csmith1188/eBankMachine/Schematics/kicad/eBankMachine.kicad_pcb

## KiCad design hardware/kicad/boards/07_alu/07_alu.kicad_pcb

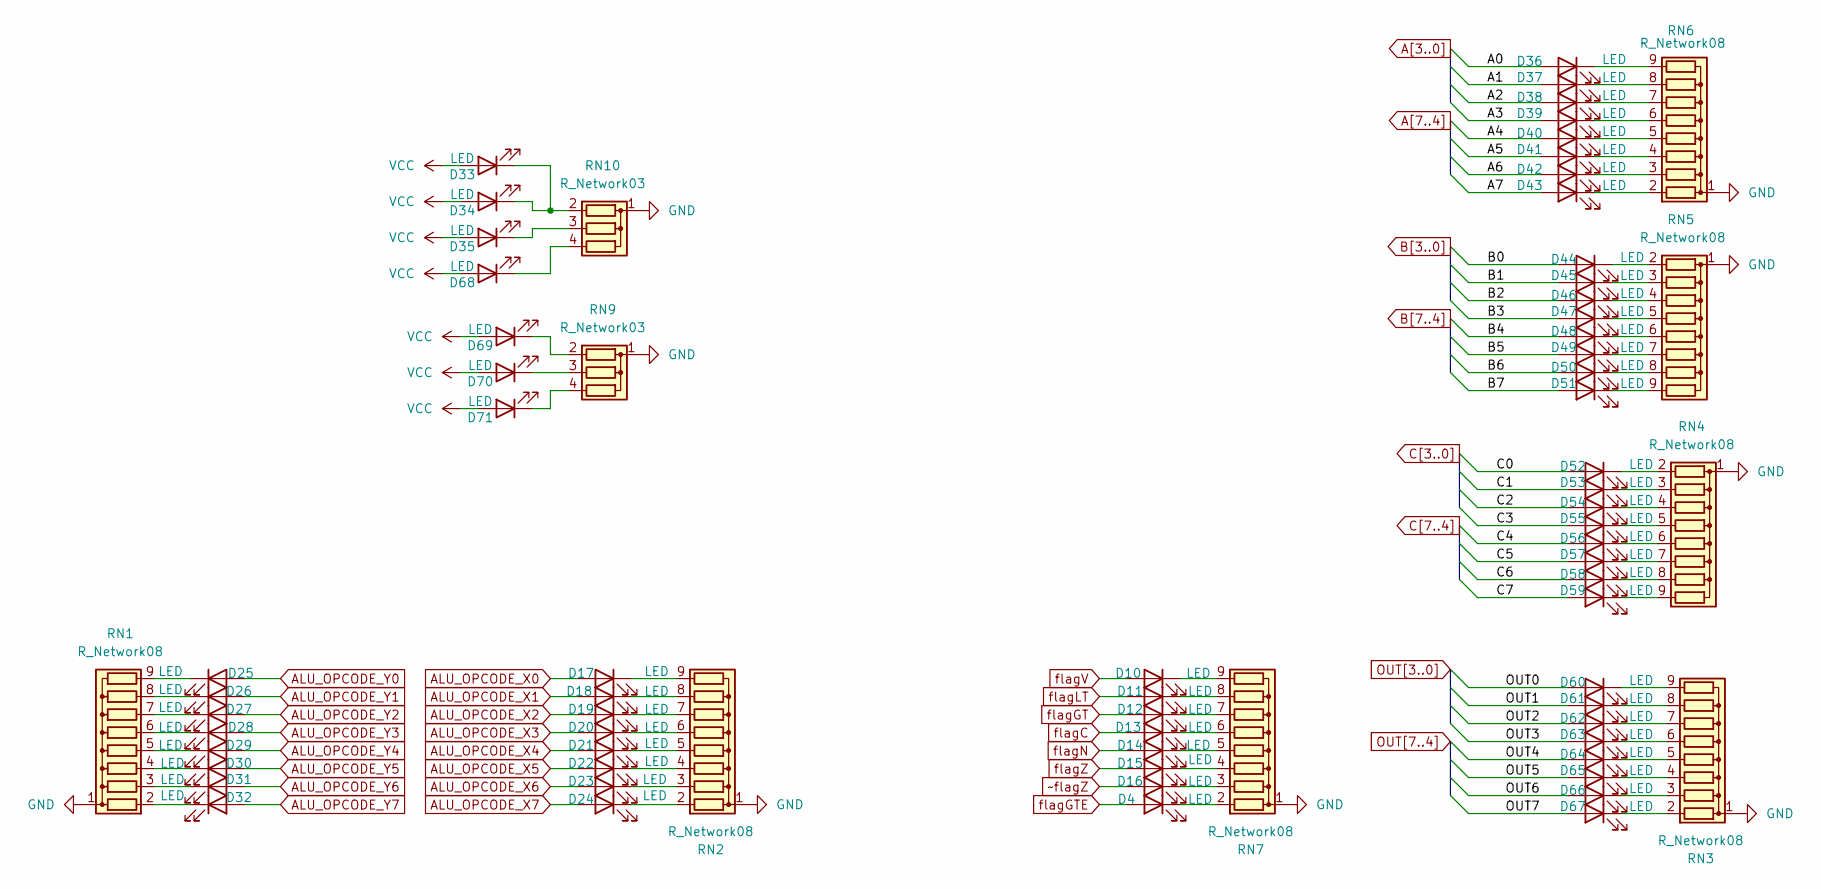
[picture p12: schematic led_unit.kicad_sch]

Parts:
D4, D10, D11, D12, D13, D14, D15, D16, D17, D18, D19, D20, D21, D22, D23, D24, D25, D26, D27, D28, D29, D30, D31, D32, D33, D34, D35, D36, D37, D38, D39, D40, D41, D42, D43, D44, D45, D46, D47, D48, D49, D50, D51, D52, D53, D54, D55, D56, D57, D58, D59, D60, D61, D62, D63, D64, D65, D66, D67, D68, D69, D70, D71: LED; LED_0805_2012Metric
RN1, RN2, RN3, RN4, RN5, RN6, RN7: R_Network08; R_Array_SIP9
RN9, RN10: R_Network03; R_Array_SIP4

Connections:
A0: D36.2 (A); also elsewhere on the board
A1: D37.2 (A); also elsewhere on the board
A2: D38.2 (A); also elsewhere on the board
A3: D39.2 (A); also elsewhere on the board
A4: D40.2 (A); also elsewhere on the board
A5: D41.2 (A); also elsewhere on the board
A6: D42.2 (A); also elsewhere on the board
A7: D43.2 (A); also elsewhere on the board
ALU_OPCODE_X0: D17.2 (A); also elsewhere on the board
ALU_OPCODE_X1: D18.2 (A); also elsewhere on the board
ALU_OPCODE_X2: D19.2 (A); also elsewhere on the board
ALU_OPCODE_X3: D20.2 (A); also elsewhere on the board
ALU_OPCODE_X4: D21.2 (A); also elsewhere on the board
ALU_OPCODE_X5: D22.2 (A); also elsewhere on the board
ALU_OPCODE_X6: D23.2 (A); also elsewhere on the board
ALU_OPCODE_X7: D24.2 (A); also elsewhere on the board
ALU_OPCODE_Y0: D25.2 (A); also elsewhere on the board
ALU_OPCODE_Y1: D26.2 (A); also elsewhere on the board
ALU_OPCODE_Y2: D27.2 (A); also elsewhere on the board
ALU_OPCODE_Y3: D28.2 (A); also elsewhere on the board
ALU_OPCODE_Y4: D29.2 (A); also elsewhere on the board
ALU_OPCODE_Y5: D30.2 (A); also elsewhere on the board
ALU_OPCODE_Y6: D31.2 (A); also elsewhere on the board
ALU_OPCODE_Y7: D32.2 (A); also elsewhere on the board
B0: D44.2 (A); also elsewhere on the board
B1: D45.2 (A); also elsewhere on the board
B2: D46.2 (A); also elsewhere on the board
B3: D47.2 (A); also elsewhere on the board
B4: D48.2 (A); also elsewhere on the board
B5: D49.2 (A); also elsewhere on the board
B6: D50.2 (A); also elsewhere on the board
B7: D51.2 (A); also elsewhere on the board
C0: D52.2 (A); also elsewhere on the board
C1: D53.2 (A); also elsewhere on the board
C2: D54.2 (A); also elsewhere on the board
C3: D55.2 (A); also elsewhere on the board
C4: D56.2 (A); also elsewhere on the board
C5: D57.2 (A); also elsewhere on the board
C6: D58.2 (A); also elsewhere on the board
C7: D59.2 (A); also elsewhere on the board
GND: RN1.1 (common), RN2.1 (common), RN3.1 (common), RN4.1 (common), RN5.1 (common), RN6.1 (common), RN7.1 (common), RN9.1 (common), RN10.1 (common); also elsewhere on the board
unnamed: D4.1 (K), RN7.2 (R1)
unnamed: D10.1 (K), RN7.9 (R8)
unnamed: D11.1 (K), RN7.8 (R7)
unnamed: D12.1 (K), RN7.7 (R6)
unnamed: D13.1 (K), RN7.6 (R5)
unnamed: D14.1 (K), RN7.5 (R4)
unnamed: D15.1 (K), RN7.4 (R3)
unnamed: D16.1 (K), RN7.3 (R2)
unnamed: D17.1 (K), RN2.9 (R8)
unnamed: D18.1 (K), RN2.8 (R7)
unnamed: D19.1 (K), RN2.7 (R6)
unnamed: D20.1 (K), RN2.6 (R5)
unnamed: D21.1 (K), RN2.5 (R4)
unnamed: D22.1 (K), RN2.4 (R3)
unnamed: D23.1 (K), RN2.3 (R2)
unnamed: D24.1 (K), RN2.2 (R1)
unnamed: D25.1 (K), RN1.9 (R8)
unnamed: D26.1 (K), RN1.8 (R7)
unnamed: D27.1 (K), RN1.7 (R6)
unnamed: D28.1 (K), RN1.6 (R5)
unnamed: D29.1 (K), RN1.5 (R4)
unnamed: D30.1 (K), RN1.4 (R3)
unnamed: D31.1 (K), RN1.3 (R2)
unnamed: D32.1 (K), RN1.2 (R1)
unnamed: D33.1 (K), D34.1 (K), RN10.2 (R1)
unnamed: D35.1 (K), RN10.3 (R2)
unnamed: D36.1 (K), RN6.9 (R8)
unnamed: D37.1 (K), RN6.8 (R7)
unnamed: D38.1 (K), RN6.7 (R6)
unnamed: D39.1 (K), RN6.6 (R5)
unnamed: D40.1 (K), RN6.5 (R4)
unnamed: D41.1 (K), RN6.4 (R3)
unnamed: D42.1 (K), RN6.3 (R2)
unnamed: D43.1 (K), RN6.2 (R1)
unnamed: D44.1 (K), RN5.2 (R1)
unnamed: D45.1 (K), RN5.3 (R2)
unnamed: D46.1 (K), RN5.4 (R3)
unnamed: D47.1 (K), RN5.5 (R4)
unnamed: D48.1 (K), RN5.6 (R5)
unnamed: D49.1 (K), RN5.7 (R6)
unnamed: D50.1 (K), RN5.8 (R7)
unnamed: D51.1 (K), RN5.9 (R8)
unnamed: D52.1 (K), RN4.2 (R1)
unnamed: D53.1 (K), RN4.3 (R2)
unnamed: D54.1 (K), RN4.4 (R3)
unnamed: D55.1 (K), RN4.5 (R4)
unnamed: D56.1 (K), RN4.6 (R5)
unnamed: D57.1 (K), RN4.7 (R6)
unnamed: D58.1 (K), RN4.8 (R7)
unnamed: D59.1 (K), RN4.9 (R8)
unnamed: D60.1 (K), RN3.9 (R8)
unnamed: D61.1 (K), RN3.8 (R7)
unnamed: D62.1 (K), RN3.7 (R6)
unnamed: D63.1 (K), RN3.6 (R5)
unnamed: D64.1 (K), RN3.5 (R4)
unnamed: D65.1 (K), RN3.4 (R3)
unnamed: D66.1 (K), RN3.3 (R2)
unnamed: D67.1 (K), RN3.2 (R1)
unnamed: D68.1 (K), RN10.4 (R3)
unnamed: D69.1 (K), RN9.2 (R1)
unnamed: D70.1 (K), RN9.3 (R2)
unnamed: D71.1 (K), RN9.4 (R3)
OUT0: D60.2 (A); also elsewhere on the board
OUT1: D61.2 (A); also elsewhere on the board
OUT2: D62.2 (A); also elsewhere on the board
OUT3: D63.2 (A); also elsewhere on the board
OUT4: D64.2 (A); also elsewhere on the board
OUT5: D65.2 (A); also elsewhere on the board
OUT6: D66.2 (A); also elsewhere on the board
OUT7: D67.2 (A); also elsewhere on the board
VCC: D33.2 (A), D34.2 (A), D35.2 (A), D68.2 (A), D69.2 (A), D70.2 (A), D71.2 (A); also elsewhere on the board
flagC: D13.2 (A); also elsewhere on the board
flagGT: D12.2 (A); also elsewhere on the board
flagGTE: D4.2 (A); also elsewhere on the board
flagLT: D11.2 (A); also elsewhere on the board
flagN: D14.2 (A); also elsewhere on the board
flagV: D10.2 (A); also elsewhere on the board
flagZ: D15.2 (A); also elsewhere on the board
~flagZ: D16.2 (A); also elsewhere on the board

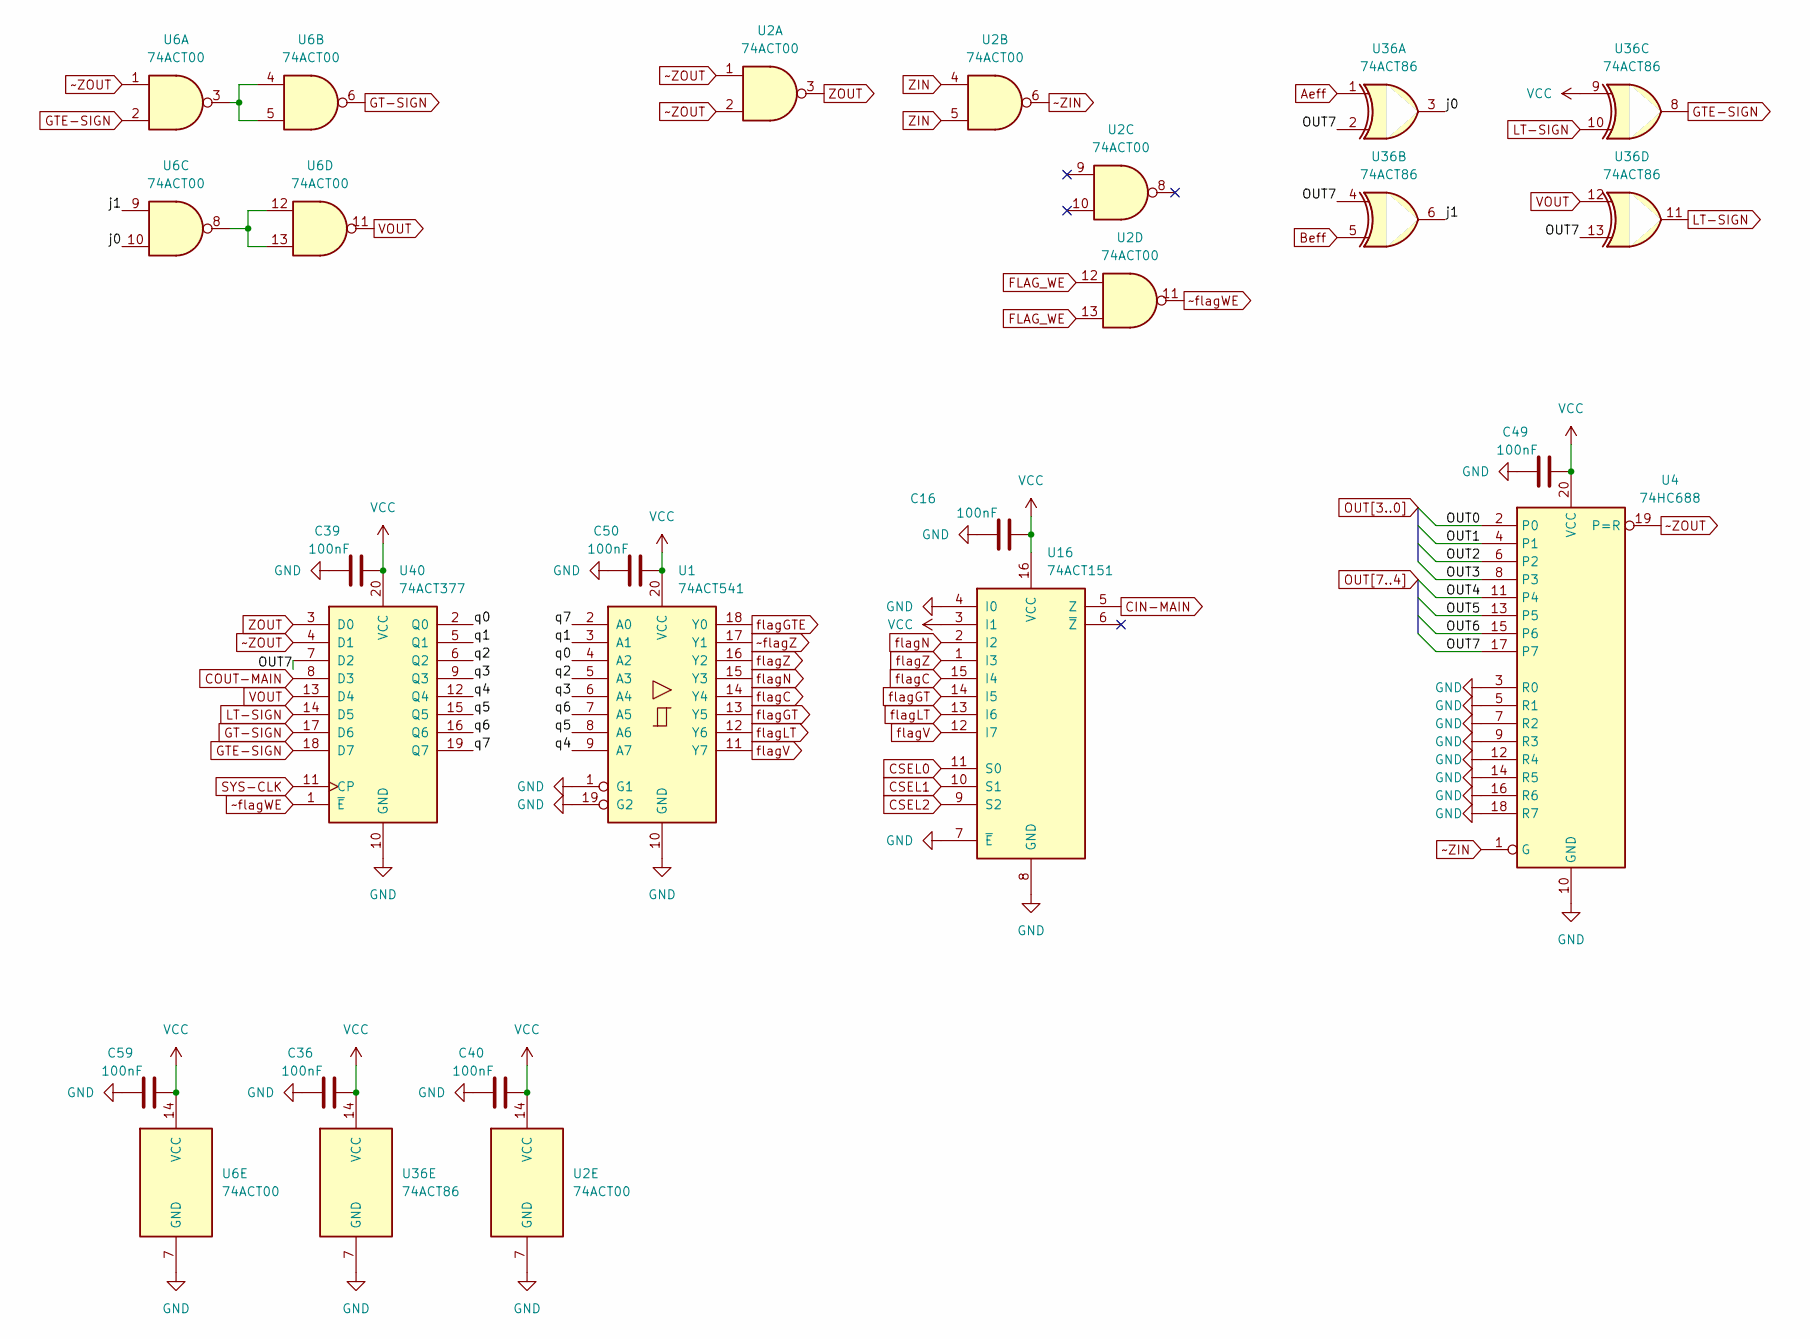
[picture p13: schematic flags_logic.kicad_sch]

Parts:
C16, C36, C39, C40, C49, C50, C59: 100nF; C_0603_1608Metric
U1: 74ACT541; SOIC-20W_7.5x12.8mm_P1.27mm
U2, U6: 74ACT00; SOIC-14_3.9x8.7mm_P1.27mm
U4: 74HC688; SOIC-20W_7.5x12.8mm_P1.27mm
U16: 74ACT151; SOIC-16_3.9x9.9mm_P1.27mm
U36: 74ACT86; SOIC-14_3.9x8.7mm_P1.27mm
U40: 74ACT377; SOIC-20W_7.5x12.8mm_P1.27mm

Connections:
/flags_logic/j0: U6.10, U36.3
/flags_logic/j1: U6.9, U36.6
/flags_logic/q0: U1.4 (A2), U40.2 (Q0)
/flags_logic/q1: U1.3 (A1), U40.5 (Q1)
/flags_logic/q2: U1.5 (A3), U40.6 (Q2)
/flags_logic/q3: U1.6 (A4), U40.9 (Q3)
/flags_logic/q4: U1.9 (A7), U40.12 (Q4)
/flags_logic/q5: U1.8 (A6), U40.15 (Q5)
/flags_logic/q6: U1.7 (A5), U40.16 (Q6)
/flags_logic/q7: U1.2 (A0), U40.19 (Q7)
Aeff: U36.1; also elsewhere on the board
Beff: U36.5; also elsewhere on the board
CIN-MAIN: U16.5 (Z); also elsewhere on the board
COUT-MAIN: U40.8 (D3); also elsewhere on the board
CSEL0: U16.11 (S0); also elsewhere on the board
CSEL1: U16.10 (S1); also elsewhere on the board
CSEL2: U16.9 (S2); also elsewhere on the board
FLAG_WE: U2.12, U2.13; also elsewhere on the board
GND: C16.1, C36.1, C39.1, C40.1, C49.1, C50.1, C59.1, U1.1 (G1), U1.10 (GND), U1.19 (G2), U2.7 (GND), U4.3 (R0), U4.5 (R1), U4.7 (R2), U4.9 (R3), U4.10 (GND), U4.12 (R4), U4.14 (R5), U4.16 (R6), U4.18 (R7), U6.7 (GND), U16.4 (I0), U16.7 (~E), U16.8 (GND), U36.7 (GND), U40.10 (GND); also elsewhere on the board
GT-SIGN: U6.6, U40.17 (D6)
GTE-SIGN: U6.2, U36.8, U40.18 (D7)
LT-SIGN: U36.10, U36.11, U40.14 (D5)
unnamed: U6.3, U6.4, U6.5
unnamed: U6.8, U6.12, U6.13
OUT0: U4.2 (P0); also elsewhere on the board
OUT1: U4.4 (P1); also elsewhere on the board
OUT2: U4.6 (P2); also elsewhere on the board
OUT3: U4.8 (P3); also elsewhere on the board
OUT4: U4.11 (P4); also elsewhere on the board
OUT5: U4.13 (P5); also elsewhere on the board
OUT6: U4.15 (P6); also elsewhere on the board
OUT7: U4.17 (P7), U36.2, U36.4, U36.13, U40.7 (D2); also elsewhere on the board
SYS-CLK: U40.11 (CP); also elsewhere on the board
VCC: C16.2, C36.2, C39.2, C40.2, C49.2, C50.2, C59.2, U1.20 (VCC), U2.14 (VCC), U4.20 (VCC), U6.14 (VCC), U16.3 (I1), U16.16 (VCC), U36.9, U36.14 (VCC), U40.20 (VCC); also elsewhere on the board
VOUT: U6.11, U36.12, U40.13 (D4)
ZIN: U2.4, U2.5; also elsewhere on the board
ZOUT: U2.3, U40.3 (D0)
flagC: U1.14 (Y4), U16.15 (I4); also elsewhere on the board
flagGT: U1.13 (Y5), U16.14 (I5); also elsewhere on the board
flagGTE: U1.18 (Y0); also elsewhere on the board
flagLT: U1.12 (Y6), U16.13 (I6); also elsewhere on the board
flagN: U1.15 (Y3), U16.2 (I2); also elsewhere on the board
flagV: U1.11 (Y7), U16.12 (I7); also elsewhere on the board
flagZ: U1.16 (Y2), U16.1 (I3); also elsewhere on the board
~ZIN: U2.6, U4.1 (G)
~ZOUT: U2.1, U2.2, U4.19 (P=R), U6.1, U40.4 (D1)
~flagWE: U2.11, U40.1 (~E)
~flagZ: U1.17 (Y1); also elsewhere on the board

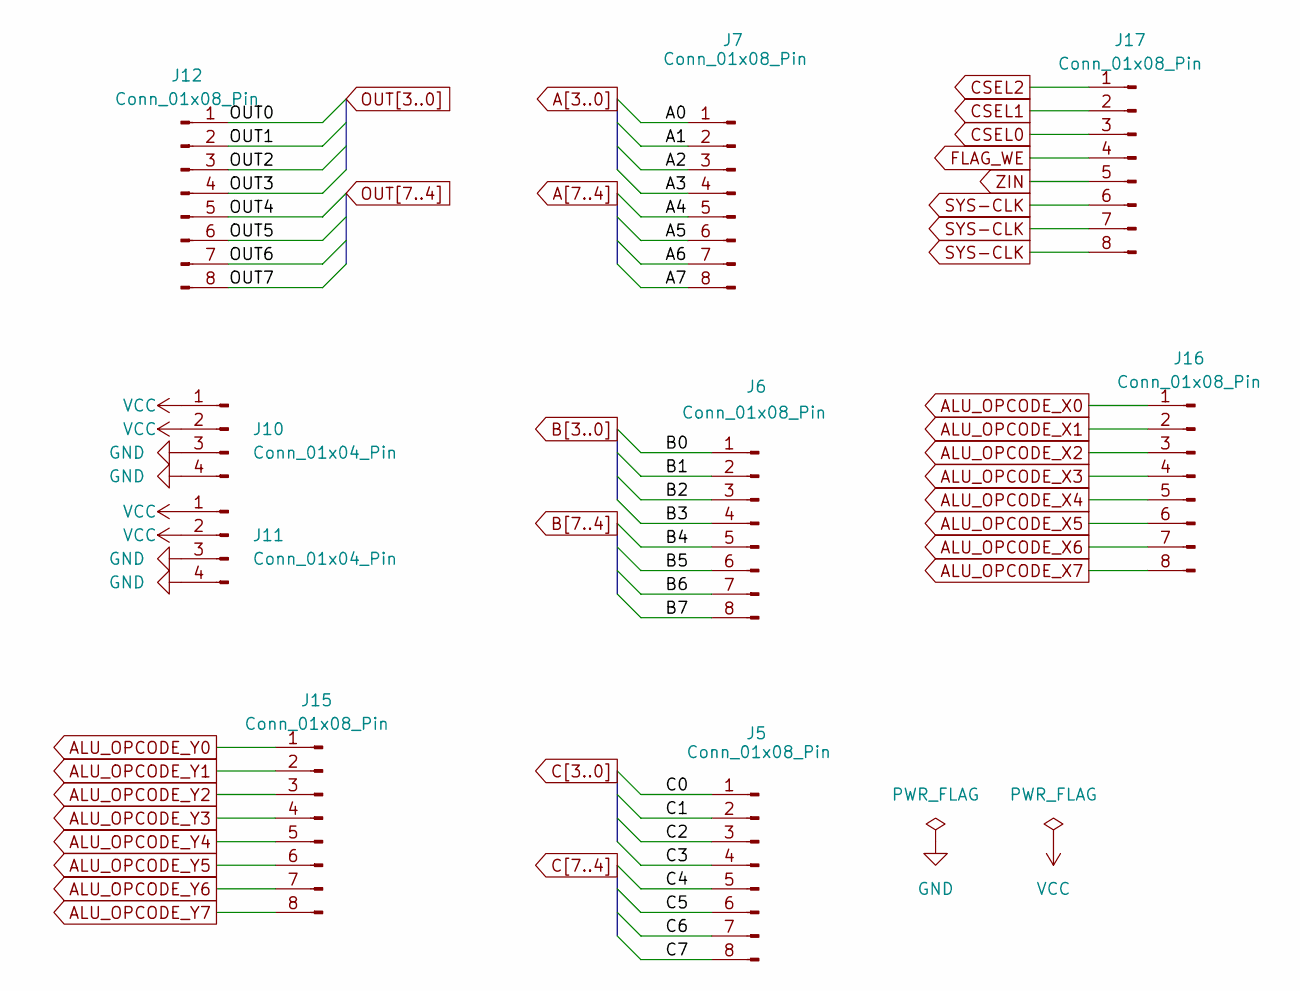
[picture p14: schematic iopins.kicad_sch]

Parts:
J5, J6, J7, J12, J15, J16, J17: Conn_01x08_Pin; PinHeader_1x08_P2.54mm_Vertical
J10, J11: Conn_01x04_Pin; PinHeader_1x04_P2.54mm_Vertical

Connections:
A0: J7.1; also elsewhere on the board
A1: J7.2; also elsewhere on the board
A2: J7.3; also elsewhere on the board
A3: J7.4; also elsewhere on the board
A4: J7.5; also elsewhere on the board
A5: J7.6; also elsewhere on the board
A6: J7.7; also elsewhere on the board
A7: J7.8; also elsewhere on the board
ALU_OPCODE_X0: J16.1; also elsewhere on the board
ALU_OPCODE_X1: J16.2; also elsewhere on the board
ALU_OPCODE_X2: J16.3; also elsewhere on the board
ALU_OPCODE_X3: J16.4; also elsewhere on the board
ALU_OPCODE_X4: J16.5; also elsewhere on the board
ALU_OPCODE_X5: J16.6; also elsewhere on the board
ALU_OPCODE_X6: J16.7; also elsewhere on the board
ALU_OPCODE_X7: J16.8; also elsewhere on the board
ALU_OPCODE_Y0: J15.1; also elsewhere on the board
ALU_OPCODE_Y1: J15.2; also elsewhere on the board
ALU_OPCODE_Y2: J15.3; also elsewhere on the board
ALU_OPCODE_Y3: J15.4; also elsewhere on the board
ALU_OPCODE_Y4: J15.5; also elsewhere on the board
ALU_OPCODE_Y5: J15.6; also elsewhere on the board
ALU_OPCODE_Y6: J15.7; also elsewhere on the board
ALU_OPCODE_Y7: J15.8; also elsewhere on the board
B0: J6.1; also elsewhere on the board
B1: J6.2; also elsewhere on the board
B2: J6.3; also elsewhere on the board
B3: J6.4; also elsewhere on the board
B4: J6.5; also elsewhere on the board
B5: J6.6; also elsewhere on the board
B6: J6.7; also elsewhere on the board
B7: J6.8; also elsewhere on the board
C0: J5.1; also elsewhere on the board
C1: J5.2; also elsewhere on the board
C2: J5.3; also elsewhere on the board
C3: J5.4; also elsewhere on the board
C4: J5.5; also elsewhere on the board
C5: J5.6; also elsewhere on the board
C6: J5.7; also elsewhere on the board
C7: J5.8; also elsewhere on the board
CSEL0: J17.3; also elsewhere on the board
CSEL1: J17.2; also elsewhere on the board
CSEL2: J17.1; also elsewhere on the board
FLAG_WE: J17.4; also elsewhere on the board
GND: J10.3, J10.4, J11.3, J11.4; also elsewhere on the board
OUT0: J12.1; also elsewhere on the board
OUT1: J12.2; also elsewhere on the board
OUT2: J12.3; also elsewhere on the board
OUT3: J12.4; also elsewhere on the board
OUT4: J12.5; also elsewhere on the board
OUT5: J12.6; also elsewhere on the board
OUT6: J12.7; also elsewhere on the board
OUT7: J12.8; also elsewhere on the board
SYS-CLK: J17.6, J17.7, J17.8; also elsewhere on the board
VCC: J10.1, J10.2, J11.1, J11.2; also elsewhere on the board
ZIN: J17.5; also elsewhere on the board

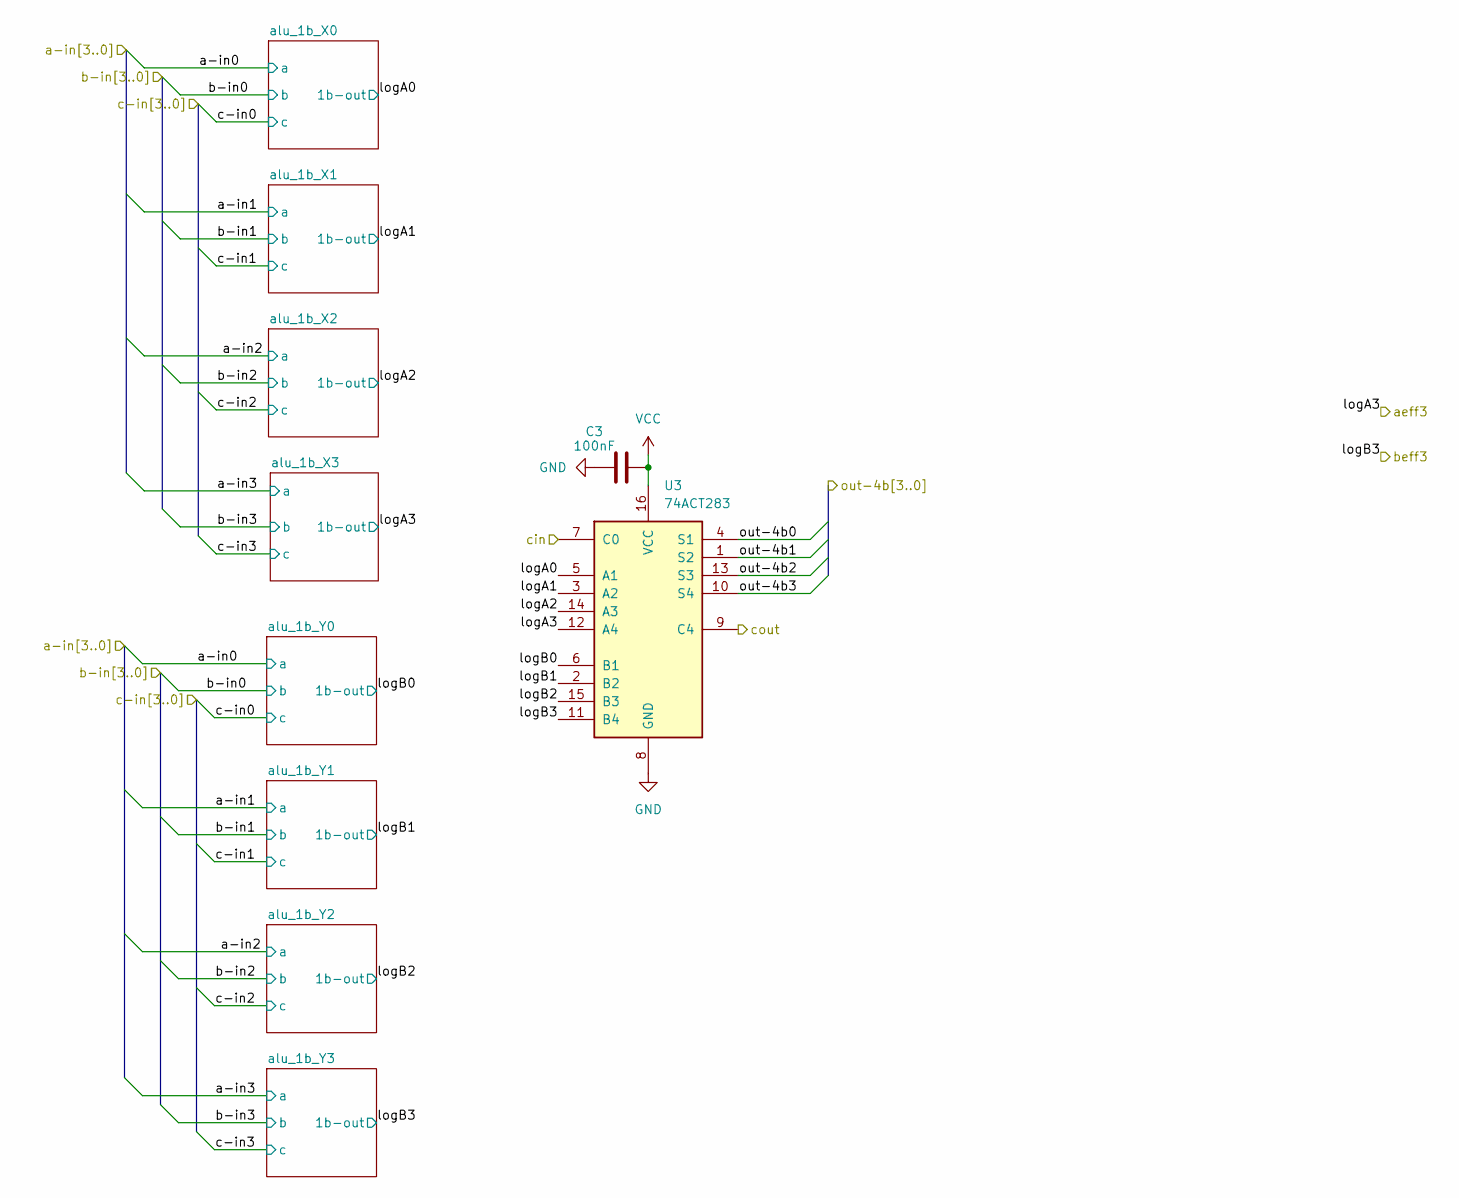
[picture p15: schematic alu_4b.kicad_sch]

Parts:
C3: 100nF; C_0603_1608Metric
U3: 74ACT283; SOIC-16_3.9x9.9mm_P1.27mm

Connections:
/alu_4b_0/cout: U3.9 (C4); also elsewhere on the board
/alu_4b_0/logA0: U3.5 (A1); also elsewhere on the board
/alu_4b_0/logA1: U3.3 (A2); also elsewhere on the board
/alu_4b_0/logA2: U3.14 (A3); also elsewhere on the board
/alu_4b_0/logA3: U3.12 (A4); also elsewhere on the board
/alu_4b_0/logB0: U3.6 (B1); also elsewhere on the board
/alu_4b_0/logB1: U3.2 (B2); also elsewhere on the board
/alu_4b_0/logB2: U3.15 (B3); also elsewhere on the board
/alu_4b_0/logB3: U3.11 (B4); also elsewhere on the board
CIN-MAIN: U3.7 (C0); also elsewhere on the board
GND: C3.1, U3.8 (GND); also elsewhere on the board
OUT0: U3.4 (S1); also elsewhere on the board
OUT1: U3.1 (S2); also elsewhere on the board
OUT2: U3.13 (S3); also elsewhere on the board
OUT3: U3.10 (S4); also elsewhere on the board
VCC: C3.2, U3.16 (VCC); also elsewhere on the board

Parts of its further copies:
C4: 100nF; C_0603_1608Metric
U5: 74ACT283; SOIC-16_3.9x9.9mm_P1.27mm

Connections of its further copies:
/alu_4b_0/cout: U5.7 (C0); also elsewhere on the board
/alu_4b_1/logA0: U5.5 (A1); also elsewhere on the board
/alu_4b_1/logA1: U5.3 (A2); also elsewhere on the board
/alu_4b_1/logA2: U5.14 (A3); also elsewhere on the board
/alu_4b_1/logB0: U5.6 (B1); also elsewhere on the board
/alu_4b_1/logB1: U5.2 (B2); also elsewhere on the board
/alu_4b_1/logB2: U5.15 (B3); also elsewhere on the board
Aeff: U5.12 (A4); also elsewhere on the board
Beff: U5.11 (B4); also elsewhere on the board
COUT-MAIN: U5.9 (C4); also elsewhere on the board
GND: C4.1, U5.8 (GND); also elsewhere on the board
OUT4: U5.4 (S1); also elsewhere on the board
OUT5: U5.1 (S2); also elsewhere on the board
OUT6: U5.13 (S3); also elsewhere on the board
OUT7: U5.10 (S4); also elsewhere on the board
VCC: C4.2, U5.16 (VCC); also elsewhere on the board

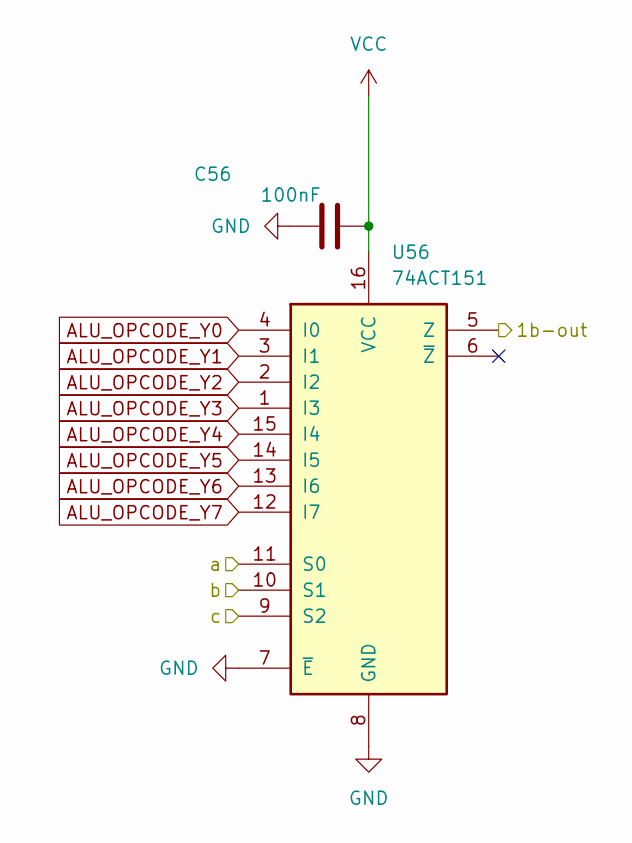
[picture p16: schematic alu_1b_Y.kicad_sch]

Parts:
C56: 100nF; C_0603_1608Metric
U56: 74ACT151; SOIC-16_3.9x9.9mm_P1.27mm

Connections:
/alu_4b_1/logB1: U56.5 (Z); also elsewhere on the board
A5: U56.11 (S0); also elsewhere on the board
ALU_OPCODE_Y0: U56.4 (I0); also elsewhere on the board
ALU_OPCODE_Y1: U56.3 (I1); also elsewhere on the board
ALU_OPCODE_Y2: U56.2 (I2); also elsewhere on the board
ALU_OPCODE_Y3: U56.1 (I3); also elsewhere on the board
ALU_OPCODE_Y4: U56.15 (I4); also elsewhere on the board
ALU_OPCODE_Y5: U56.14 (I5); also elsewhere on the board
ALU_OPCODE_Y6: U56.13 (I6); also elsewhere on the board
ALU_OPCODE_Y7: U56.12 (I7); also elsewhere on the board
B5: U56.10 (S1); also elsewhere on the board
C5: U56.9 (S2); also elsewhere on the board
GND: C56.1, U56.7 (~E), U56.8 (GND); also elsewhere on the board
VCC: C56.2, U56.16 (VCC); also elsewhere on the board

Parts of its further copies:
C41, C42, C43, C44, C55, C57, C58: 100nF; C_0603_1608Metric
U41, U42, U43, U44, U53, U54, U55: 74ACT151; SOIC-16_3.9x9.9mm_P1.27mm

Connections of its further copies:
/alu_4b_0/logB0: U41.5 (Z); also elsewhere on the board
/alu_4b_0/logB1: U42.5 (Z); also elsewhere on the board
/alu_4b_0/logB2: U43.5 (Z); also elsewhere on the board
/alu_4b_0/logB3: U44.5 (Z); also elsewhere on the board
/alu_4b_1/logB0: U53.5 (Z); also elsewhere on the board
/alu_4b_1/logB2: U54.5 (Z); also elsewhere on the board
A0: U41.11 (S0); also elsewhere on the board
A1: U42.11 (S0); also elsewhere on the board
A2: U43.11 (S0); also elsewhere on the board
A3: U44.11 (S0); also elsewhere on the board
A4: U53.11 (S0); also elsewhere on the board
A6: U54.11 (S0); also elsewhere on the board
A7: U55.11 (S0); also elsewhere on the board
ALU_OPCODE_Y0: U41.4 (I0), U42.4 (I0), U43.4 (I0), U44.4 (I0), U53.4 (I0), U54.4 (I0), U55.4 (I0); also elsewhere on the board
ALU_OPCODE_Y1: U41.3 (I1), U42.3 (I1), U43.3 (I1), U44.3 (I1), U53.3 (I1), U54.3 (I1), U55.3 (I1); also elsewhere on the board
ALU_OPCODE_Y2: U41.2 (I2), U42.2 (I2), U43.2 (I2), U44.2 (I2), U53.2 (I2), U54.2 (I2), U55.2 (I2); also elsewhere on the board
ALU_OPCODE_Y3: U41.1 (I3), U42.1 (I3), U43.1 (I3), U44.1 (I3), U53.1 (I3), U54.1 (I3), U55.1 (I3); also elsewhere on the board
ALU_OPCODE_Y4: U41.15 (I4), U42.15 (I4), U43.15 (I4), U44.15 (I4), U53.15 (I4), U54.15 (I4), U55.15 (I4); also elsewhere on the board
ALU_OPCODE_Y5: U41.14 (I5), U42.14 (I5), U43.14 (I5), U44.14 (I5), U53.14 (I5), U54.14 (I5), U55.14 (I5); also elsewhere on the board
ALU_OPCODE_Y6: U41.13 (I6), U42.13 (I6), U43.13 (I6), U44.13 (I6), U53.13 (I6), U54.13 (I6), U55.13 (I6); also elsewhere on the board
ALU_OPCODE_Y7: U41.12 (I7), U42.12 (I7), U43.12 (I7), U44.12 (I7), U53.12 (I7), U54.12 (I7), U55.12 (I7); also elsewhere on the board
B0: U41.10 (S1); also elsewhere on the board
B1: U42.10 (S1); also elsewhere on the board
B2: U43.10 (S1); also elsewhere on the board
B3: U44.10 (S1); also elsewhere on the board
B4: U53.10 (S1); also elsewhere on the board
B6: U54.10 (S1); also elsewhere on the board
B7: U55.10 (S1); also elsewhere on the board
Beff: U55.5 (Z); also elsewhere on the board
C0: U41.9 (S2); also elsewhere on the board
C1: U42.9 (S2); also elsewhere on the board
C2: U43.9 (S2); also elsewhere on the board
C3: U44.9 (S2); also elsewhere on the board
C4: U53.9 (S2); also elsewhere on the board
C6: U54.9 (S2); also elsewhere on the board
C7: U55.9 (S2); also elsewhere on the board
GND: C41.1, C42.1, C43.1, C44.1, C55.1, C57.1, C58.1, U41.7 (~E), U41.8 (GND), U42.7 (~E), U42.8 (GND), U43.7 (~E), U43.8 (GND), U44.7 (~E), U44.8 (GND), U53.7 (~E), U53.8 (GND), U54.7 (~E), U54.8 (GND), U55.7 (~E), U55.8 (GND); also elsewhere on the board
VCC: C41.2, C42.2, C43.2, C44.2, C55.2, C57.2, C58.2, U41.16 (VCC), U42.16 (VCC), U43.16 (VCC), U44.16 (VCC), U53.16 (VCC), U54.16 (VCC), U55.16 (VCC); also elsewhere on the board

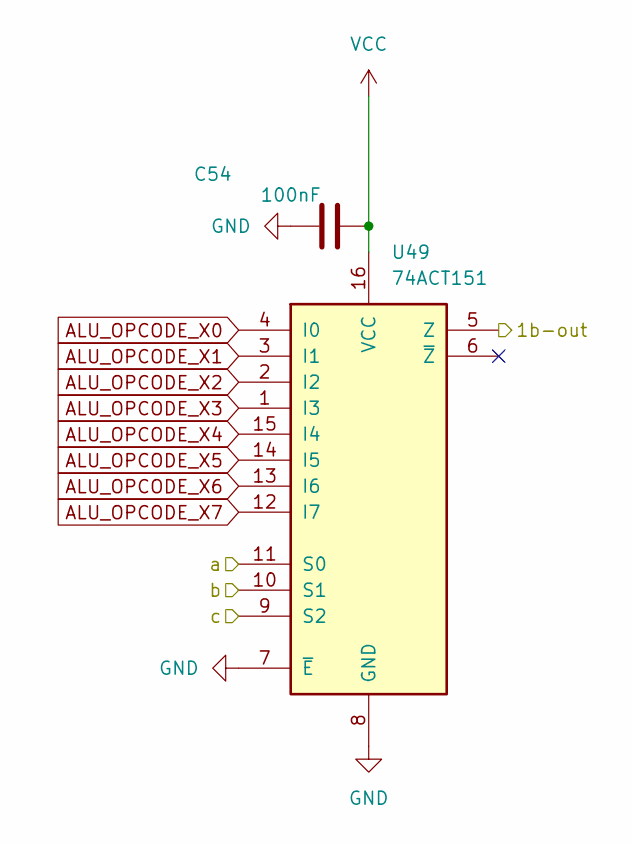
[picture p17: schematic alu_1b_X.kicad_sch]

Parts:
C54: 100nF; C_0603_1608Metric
U49: 74ACT151; SOIC-16_3.9x9.9mm_P1.27mm

Connections:
A7: U49.11 (S0); also elsewhere on the board
ALU_OPCODE_X0: U49.4 (I0); also elsewhere on the board
ALU_OPCODE_X1: U49.3 (I1); also elsewhere on the board
ALU_OPCODE_X2: U49.2 (I2); also elsewhere on the board
ALU_OPCODE_X3: U49.1 (I3); also elsewhere on the board
ALU_OPCODE_X4: U49.15 (I4); also elsewhere on the board
ALU_OPCODE_X5: U49.14 (I5); also elsewhere on the board
ALU_OPCODE_X6: U49.13 (I6); also elsewhere on the board
ALU_OPCODE_X7: U49.12 (I7); also elsewhere on the board
Aeff: U49.5 (Z); also elsewhere on the board
B7: U49.10 (S1); also elsewhere on the board
C7: U49.9 (S2); also elsewhere on the board
GND: C54.1, U49.7 (~E), U49.8 (GND); also elsewhere on the board
VCC: C54.2, U49.16 (VCC); also elsewhere on the board

Parts of its further copies:
C45, C46, C47, C48, C51, C52, C53: 100nF; C_0603_1608Metric
U45, U46, U47, U48, U50, U51, U52: 74ACT151; SOIC-16_3.9x9.9mm_P1.27mm

Connections of its further copies:
/alu_4b_0/logA0: U45.5 (Z); also elsewhere on the board
/alu_4b_0/logA1: U46.5 (Z); also elsewhere on the board
/alu_4b_0/logA2: U47.5 (Z); also elsewhere on the board
/alu_4b_0/logA3: U48.5 (Z); also elsewhere on the board
/alu_4b_1/logA0: U50.5 (Z); also elsewhere on the board
/alu_4b_1/logA1: U51.5 (Z); also elsewhere on the board
/alu_4b_1/logA2: U52.5 (Z); also elsewhere on the board
A0: U45.11 (S0); also elsewhere on the board
A1: U46.11 (S0); also elsewhere on the board
A2: U47.11 (S0); also elsewhere on the board
A3: U48.11 (S0); also elsewhere on the board
A4: U50.11 (S0); also elsewhere on the board
A5: U51.11 (S0); also elsewhere on the board
A6: U52.11 (S0); also elsewhere on the board
ALU_OPCODE_X0: U45.4 (I0), U46.4 (I0), U47.4 (I0), U48.4 (I0), U50.4 (I0), U51.4 (I0), U52.4 (I0); also elsewhere on the board
ALU_OPCODE_X1: U45.3 (I1), U46.3 (I1), U47.3 (I1), U48.3 (I1), U50.3 (I1), U51.3 (I1), U52.3 (I1); also elsewhere on the board
ALU_OPCODE_X2: U45.2 (I2), U46.2 (I2), U47.2 (I2), U48.2 (I2), U50.2 (I2), U51.2 (I2), U52.2 (I2); also elsewhere on the board
ALU_OPCODE_X3: U45.1 (I3), U46.1 (I3), U47.1 (I3), U48.1 (I3), U50.1 (I3), U51.1 (I3), U52.1 (I3); also elsewhere on the board
ALU_OPCODE_X4: U45.15 (I4), U46.15 (I4), U47.15 (I4), U48.15 (I4), U50.15 (I4), U51.15 (I4), U52.15 (I4); also elsewhere on the board
ALU_OPCODE_X5: U45.14 (I5), U46.14 (I5), U47.14 (I5), U48.14 (I5), U50.14 (I5), U51.14 (I5), U52.14 (I5); also elsewhere on the board
ALU_OPCODE_X6: U45.13 (I6), U46.13 (I6), U47.13 (I6), U48.13 (I6), U50.13 (I6), U51.13 (I6), U52.13 (I6); also elsewhere on the board
ALU_OPCODE_X7: U45.12 (I7), U46.12 (I7), U47.12 (I7), U48.12 (I7), U50.12 (I7), U51.12 (I7), U52.12 (I7); also elsewhere on the board
B0: U45.10 (S1); also elsewhere on the board
B1: U46.10 (S1); also elsewhere on the board
B2: U47.10 (S1); also elsewhere on the board
B3: U48.10 (S1); also elsewhere on the board
B4: U50.10 (S1); also elsewhere on the board
B5: U51.10 (S1); also elsewhere on the board
B6: U52.10 (S1); also elsewhere on the board
C0: U45.9 (S2); also elsewhere on the board
C1: U46.9 (S2); also elsewhere on the board
C2: U47.9 (S2); also elsewhere on the board
C3: U48.9 (S2); also elsewhere on the board
C4: U50.9 (S2); also elsewhere on the board
C5: U51.9 (S2); also elsewhere on the board
C6: U52.9 (S2); also elsewhere on the board
GND: C45.1, C46.1, C47.1, C48.1, C51.1, C52.1, C53.1, U45.7 (~E), U45.8 (GND), U46.7 (~E), U46.8 (GND), U47.7 (~E), U47.8 (GND), U48.7 (~E), U48.8 (GND), U50.7 (~E), U50.8 (GND), U51.7 (~E), U51.8 (GND), U52.7 (~E), U52.8 (GND); also elsewhere on the board
VCC: C45.2, C46.2, C47.2, C48.2, C51.2, C52.2, C53.2, U45.16 (VCC), U46.16 (VCC), U47.16 (VCC), U48.16 (VCC), U50.16 (VCC), U51.16 (VCC), U52.16 (VCC); also elsewhere on the board
