csmith1188/eBankMachine/eBankMachine/net.cpp

#include "eBankMachine.h"

void wifiEnsureConnected() {
  if (WiFi.status() == WL_CONNECTED) {
    setupWebOtaOnce();
    return;
  }

  showMsg("WiFi...", "reconnecting", 0);
  dbgPrintf("WiFi reconnect...\n");

  WiFi.disconnect(true);
  WiFi.mode(WIFI_STA);
  WiFi.setSleep(false);
  WiFi.begin(WIFI_SSID, WIFI_PASS);

  unsigned long start = millis();
  while (WiFi.status() != WL_CONNECTED && millis() - start < 12000) {
    server.handleClient();
    delay(50);
  }

  setupWebOtaOnce();
}
